jogi-k/RubberJogi/pics/Arduino_T1_to_remove.png

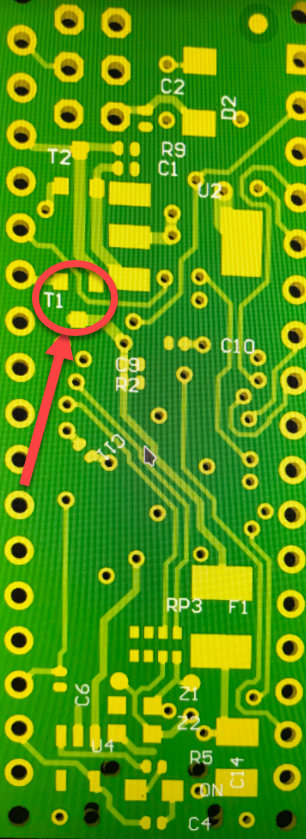
pics/Arduino_T1_to_remove.png
