jogi-k/RubberJogi/pics/RubberJogi_Aufbau.jpg

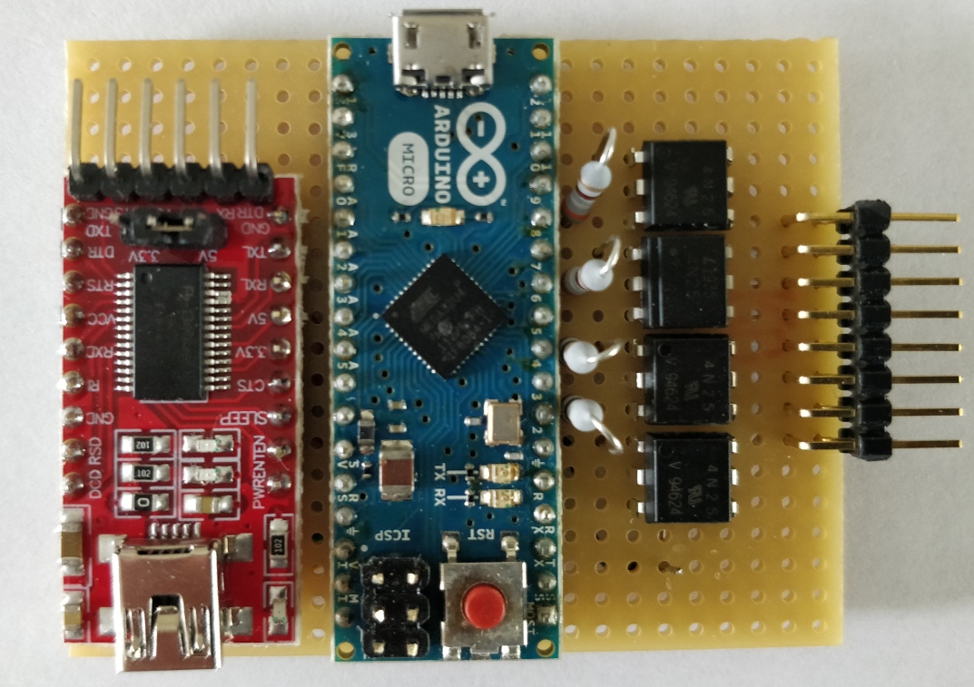
pics/RubberJogi_Aufbau.jpg
