jogi-k/RubberJogi/pics/RubberJogi_Aufbau_NoSwitch.jpg

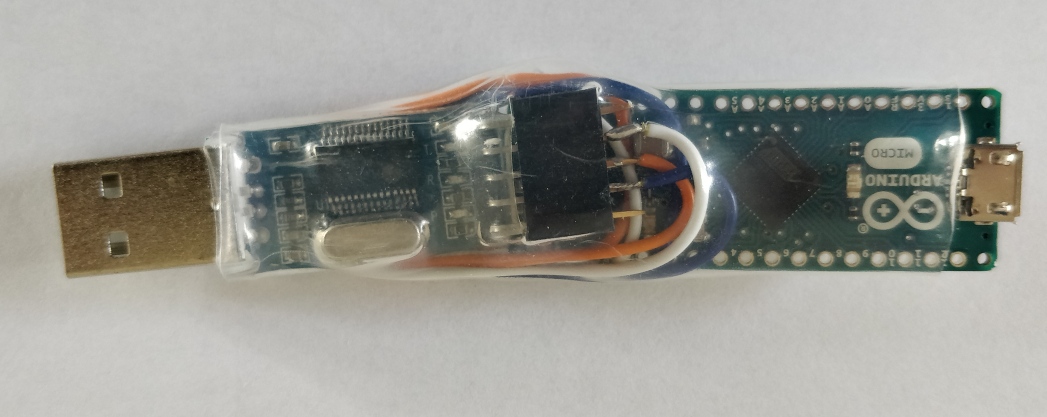
pics/RubberJogi_Aufbau_NoSwitch.jpg
